tysch/stm32-geiger/Hardware/Main PCB/Main_PCB_overview.png

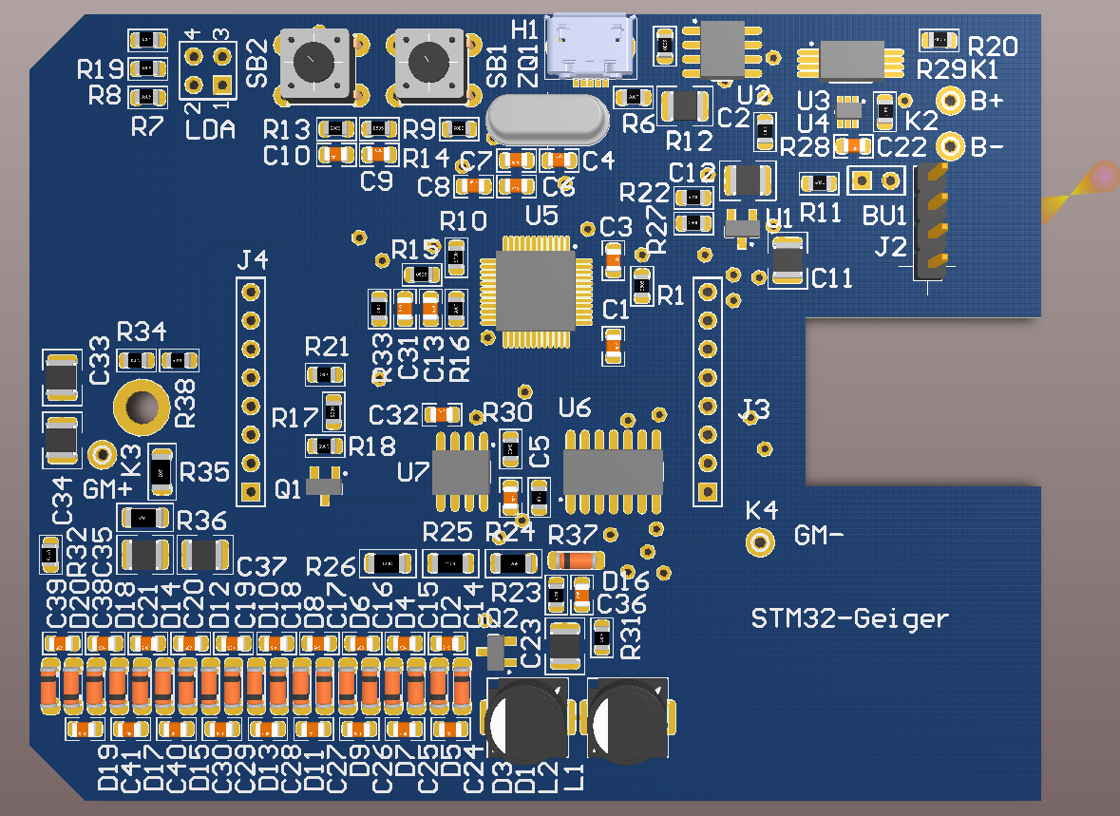
Hardware/Main PCB/Main_PCB_overview.png
