tysch/stm32-geiger/Prototyping/Case_prototype/1.jpg

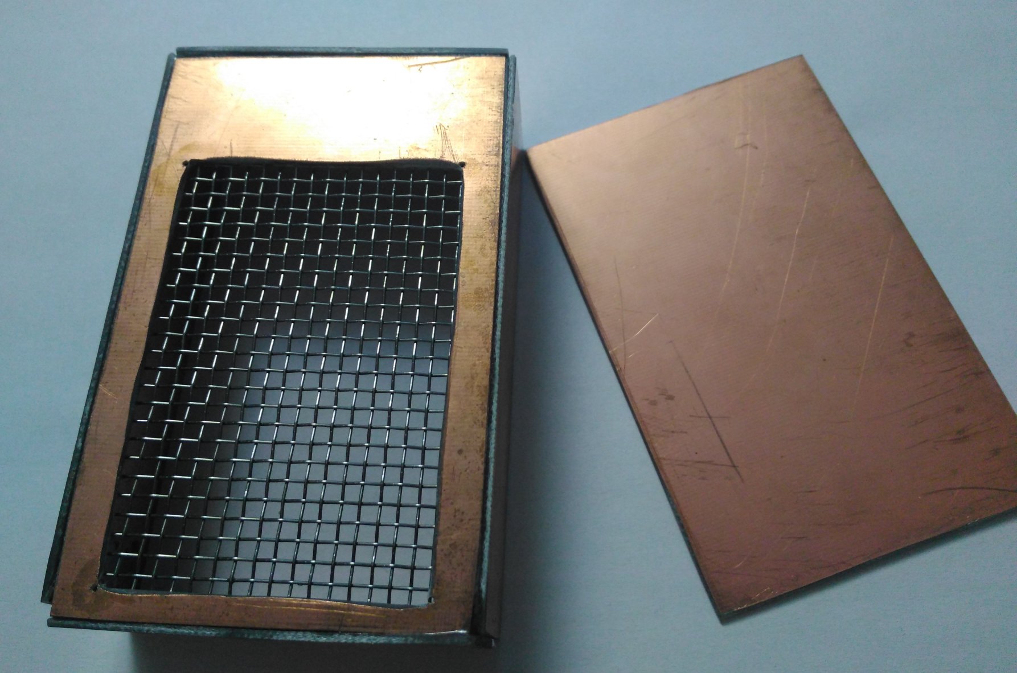
Prototyping/Case_prototype/1.jpg
