tysch/stm32-geiger/Prototyping/Case_prototype/2.jpg

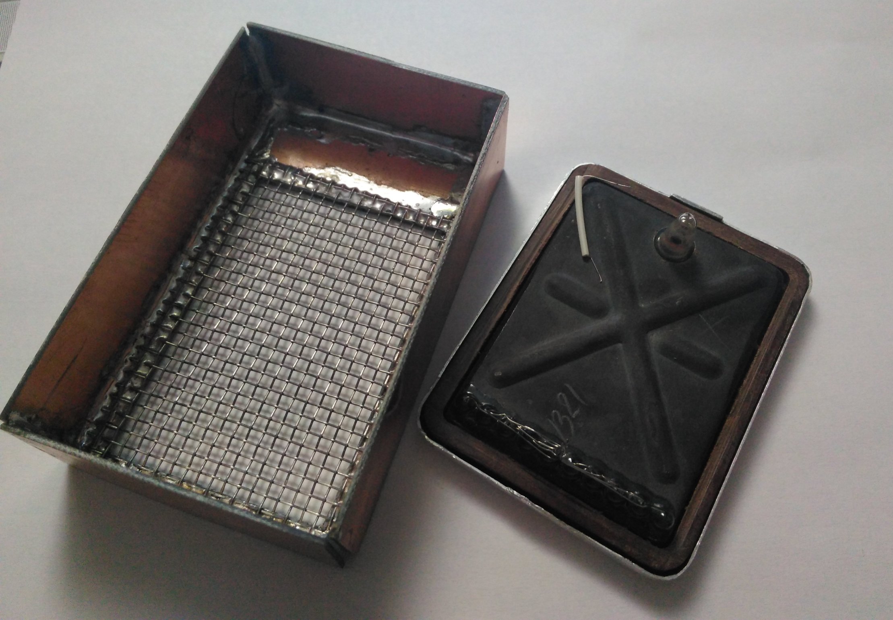
Prototyping/Case_prototype/2.jpg
