tysch/stm32-geiger/Prototyping/Case_prototype/3.jpg

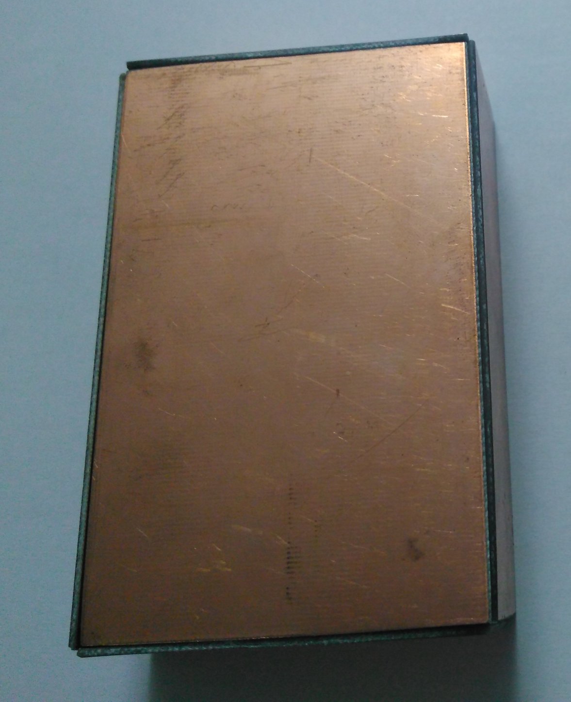
Prototyping/Case_prototype/3.jpg
