tysch/stm32-geiger/Prototyping/Case_prototype/4.jpg

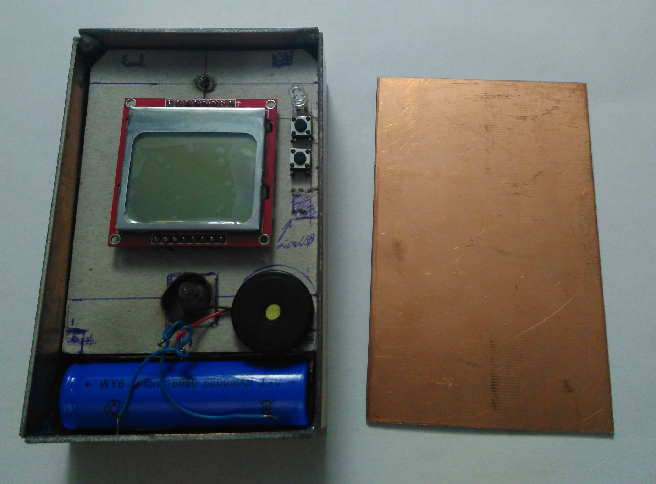
Prototyping/Case_prototype/4.jpg
