tysch/stm32-geiger/Case and assembly/1.jpg

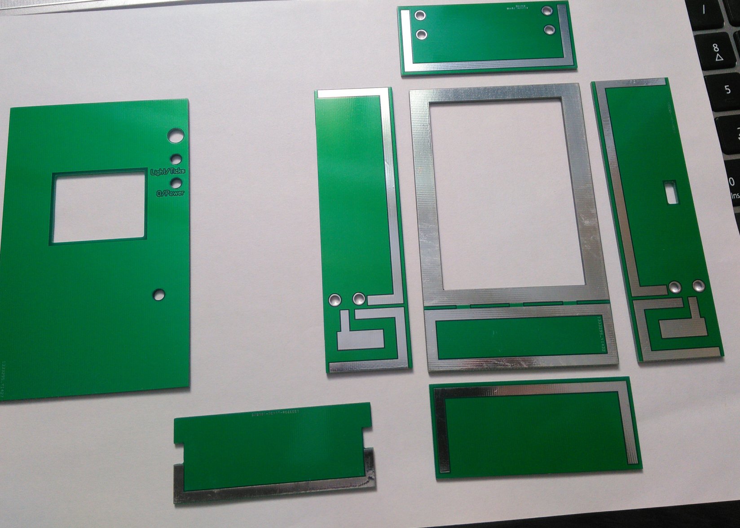
Case and assembly/1.jpg
