tysch/stm32-geiger/Case and assembly/2.jpg

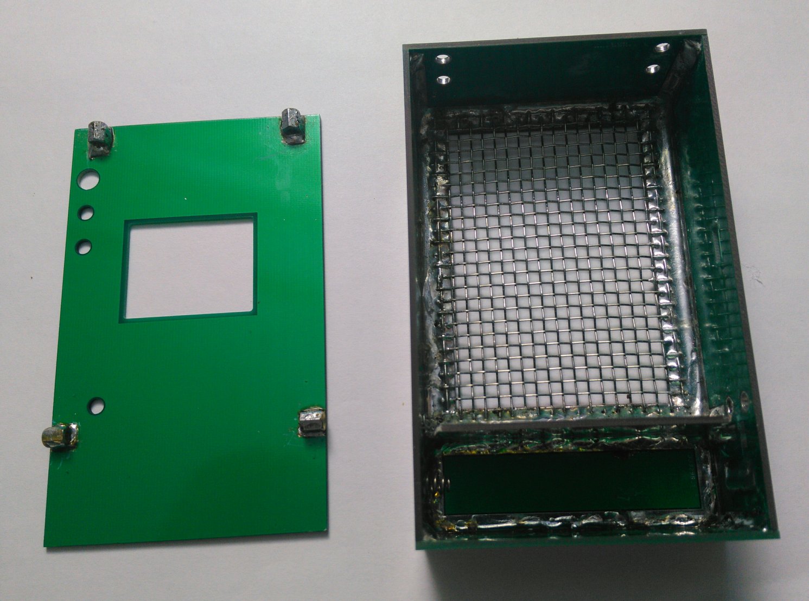
Case and assembly/2.jpg
