tysch/stm32-geiger/Case and assembly/3.jpg

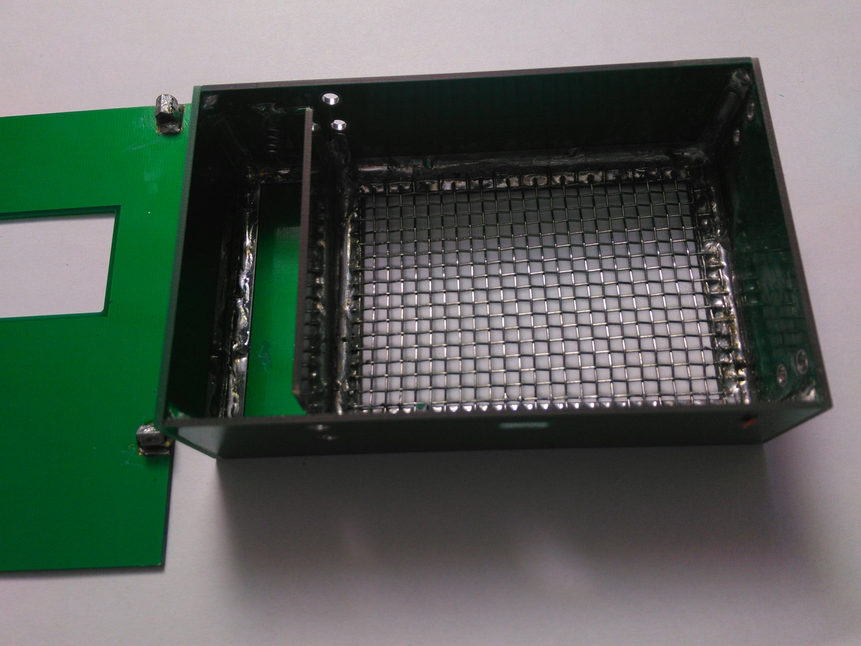
Case and assembly/3.jpg
