tysch/stm32-geiger/Case and assembly/4.jpg

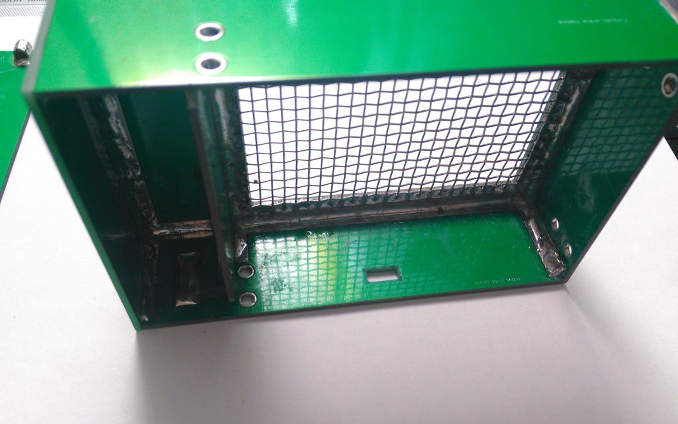
Case and assembly/4.jpg
