tysch/stm32-geiger/Case and assembly/5.jpg

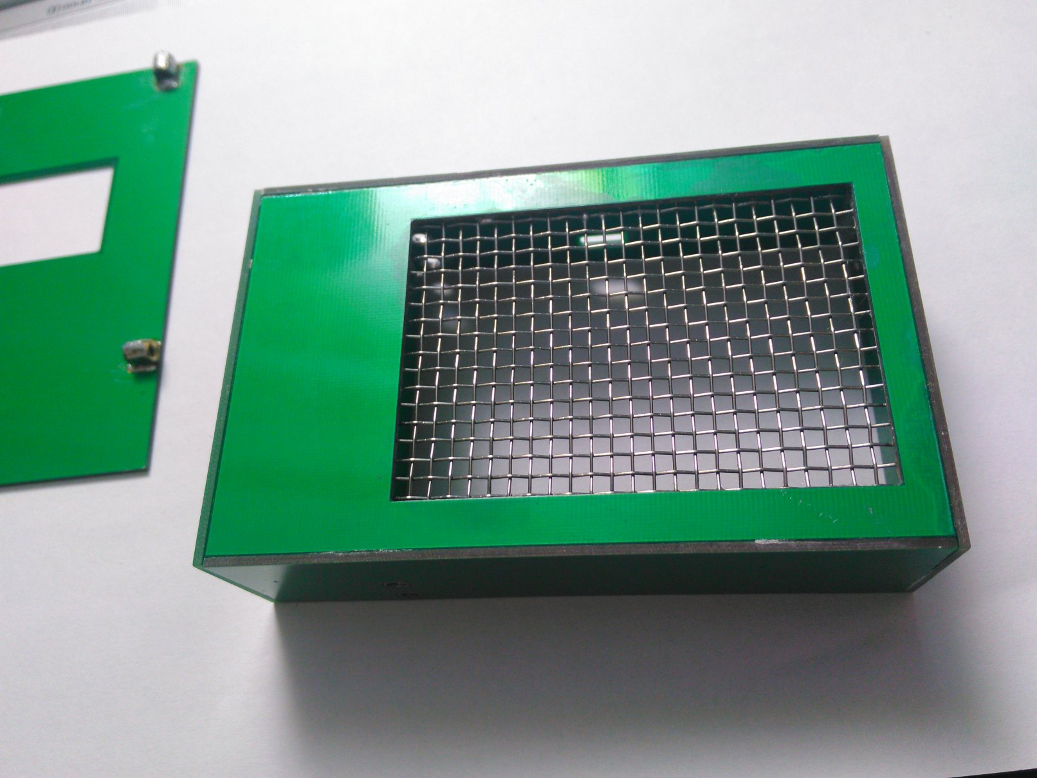
Case and assembly/5.jpg
