tysch/stm32-geiger/Case and assembly/6.jpg

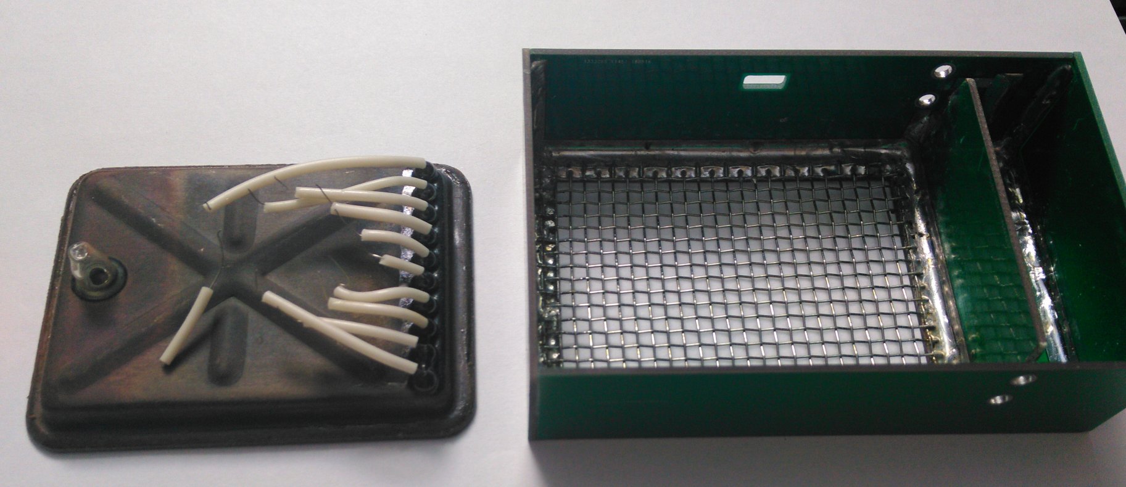
Case and assembly/6.jpg
