tysch/stm32-geiger/Case and assembly/7.jpg

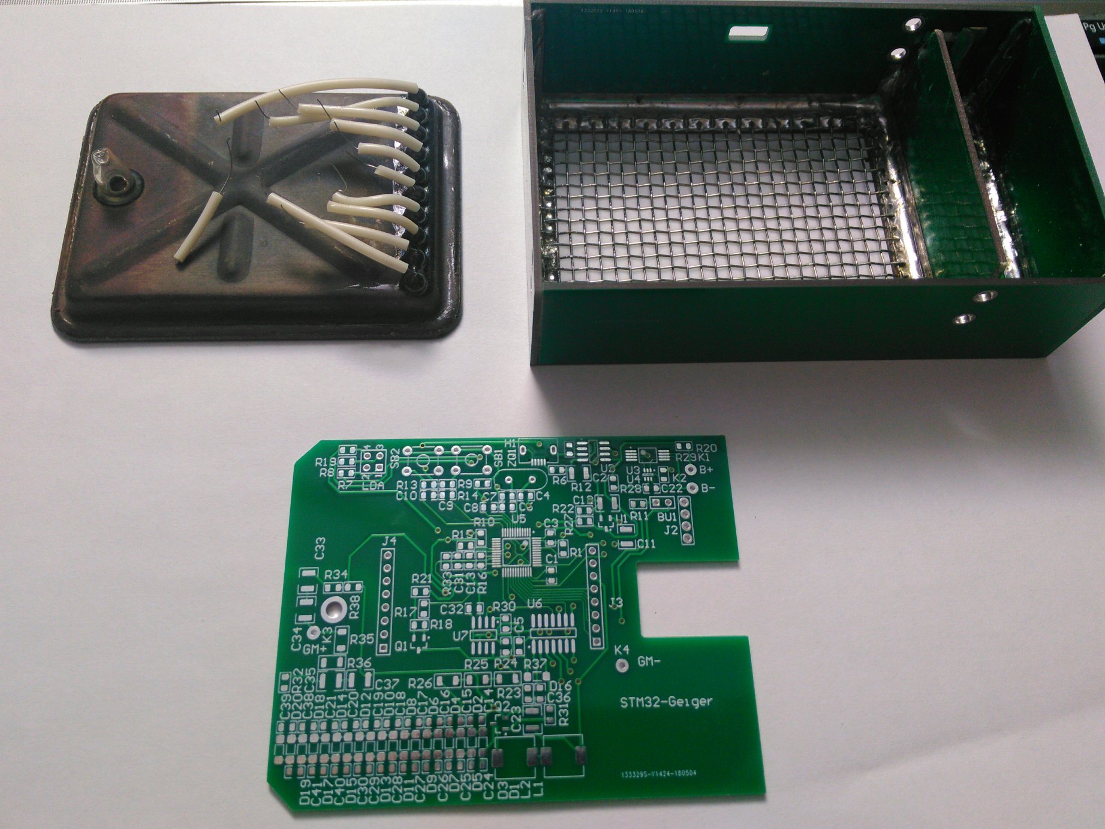
Case and assembly/7.jpg
