tysch/stm32-geiger/Case and assembly/9.jpg

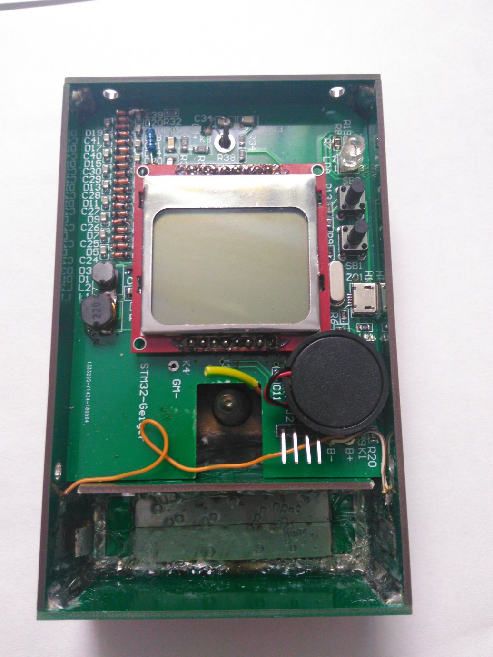
Case and assembly/9.jpg
