tysch/stm32-geiger/Case and assembly/10.jpg

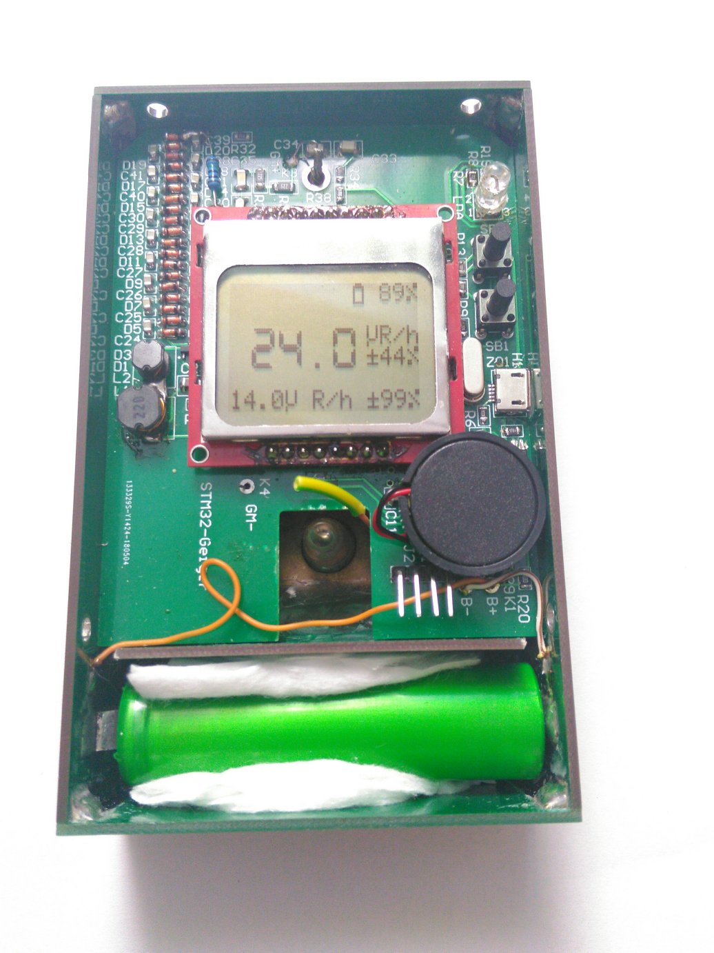
Case and assembly/10.jpg
