tysch/stm32-geiger/Case and assembly/11.jpg

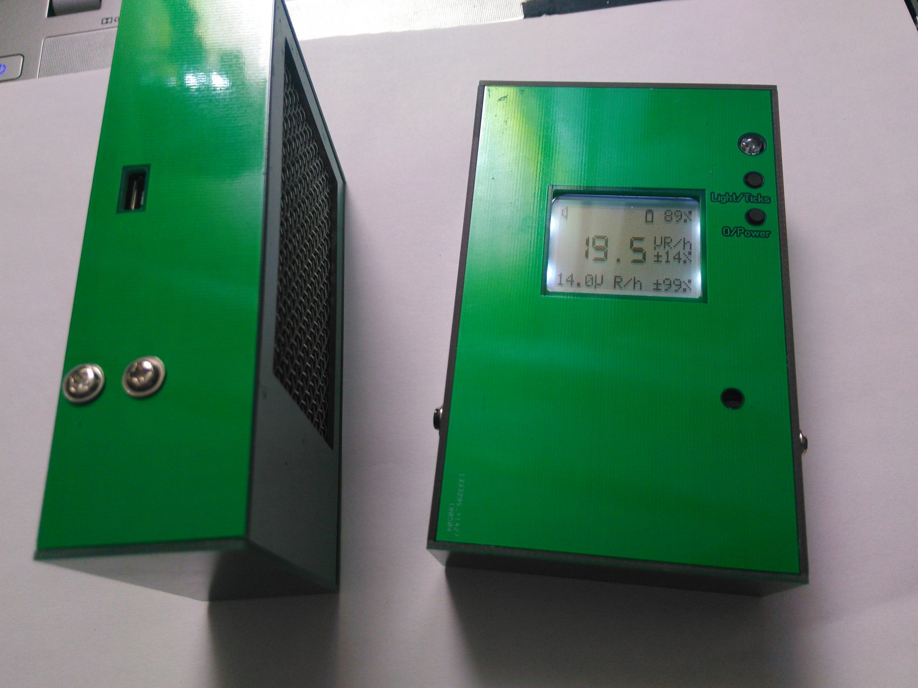
Case and assembly/11.jpg
