tysch/stm32-geiger/Case and assembly/12.jpg

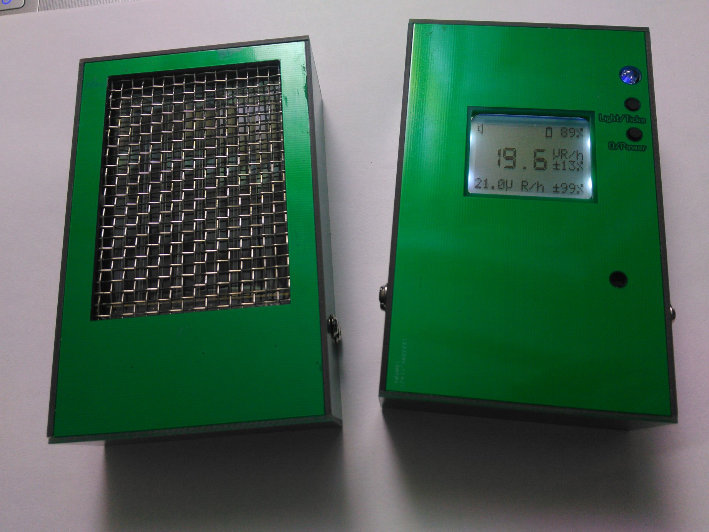
Case and assembly/12.jpg
