tysch/stm32-geiger/Case and assembly/14.jpg

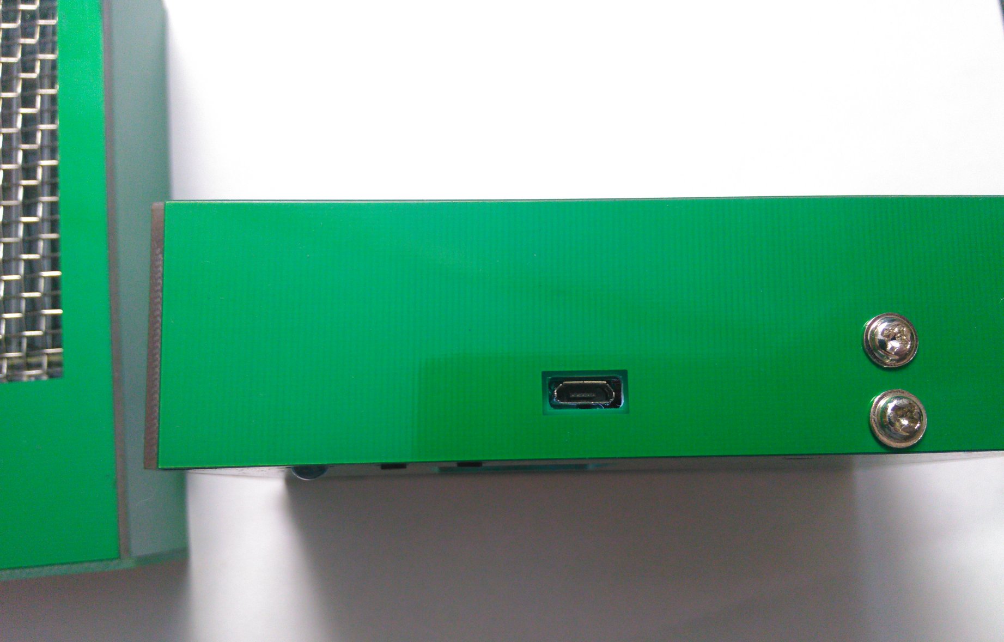
Case and assembly/14.jpg
