tysch/stm32-geiger/Case and assembly/15.jpg

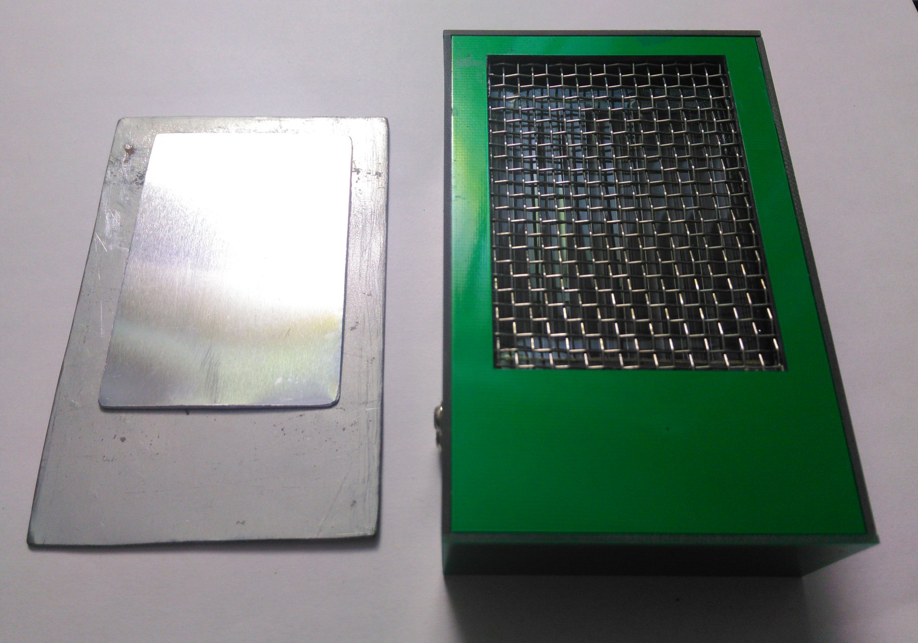
Case and assembly/15.jpg
