tysch/stm32-geiger/Case and assembly/16.jpg

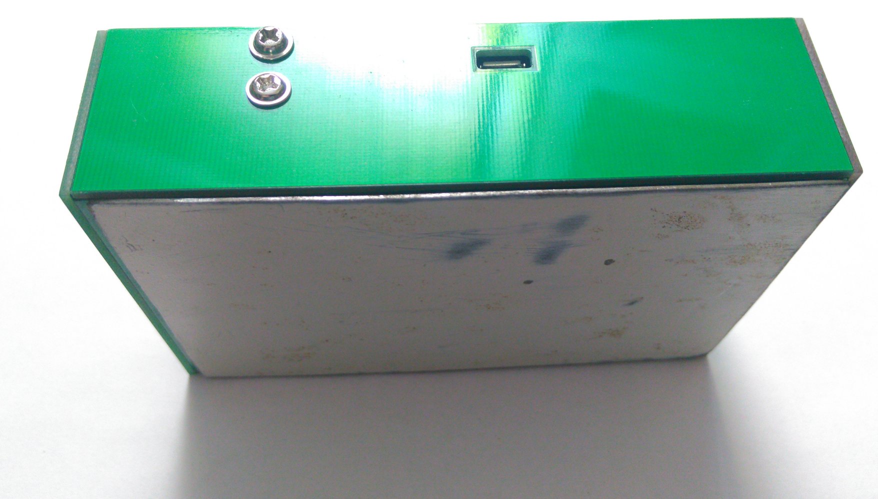
Case and assembly/16.jpg
