tysch/stm32-geiger/Case and assembly/Case_Drawing/Case_outer walls.jpg

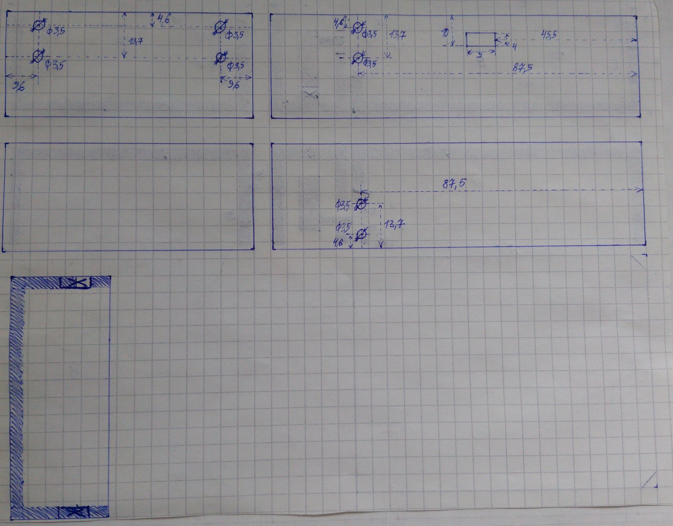
Case and assembly/Case_Drawing/Case_outer walls.jpg
