tysch/stm32-geiger/Case and assembly/Case_Drawing/Case_walls_spacer.jpg

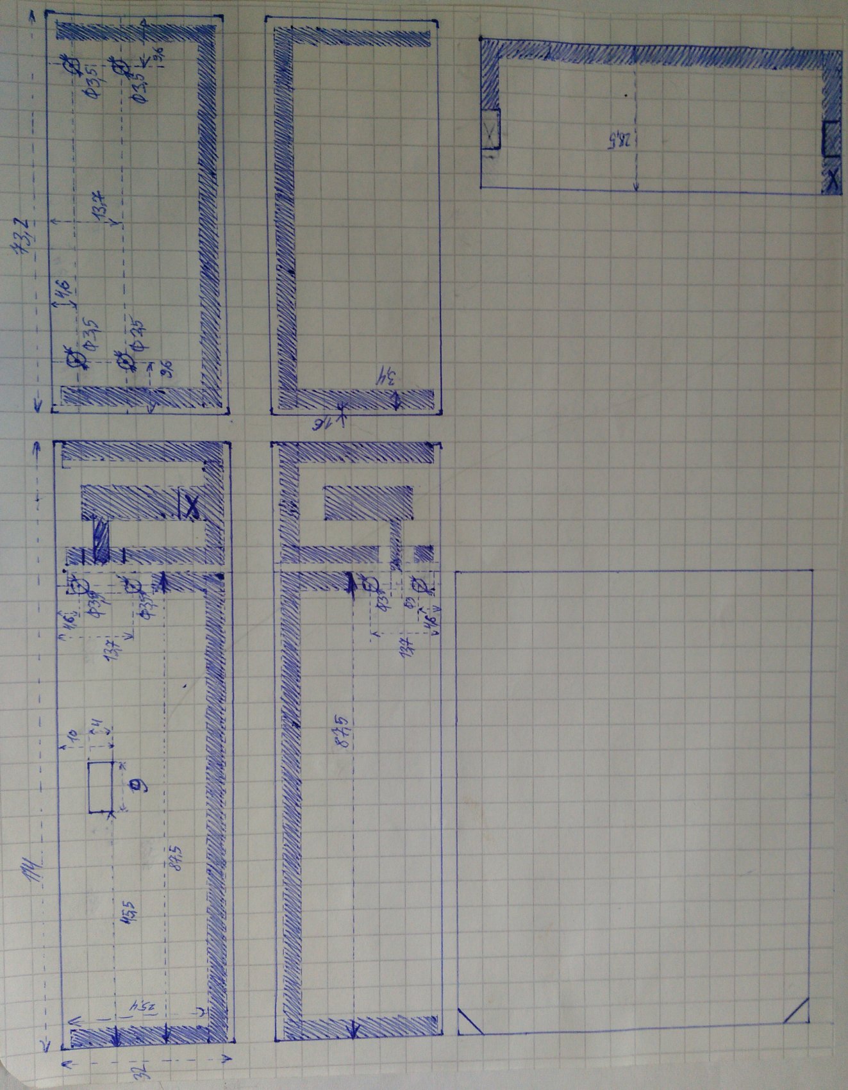
Case and assembly/Case_Drawing/Case_walls_spacer.jpg
