tysch/stm32-geiger/Test results/ambient.jpg

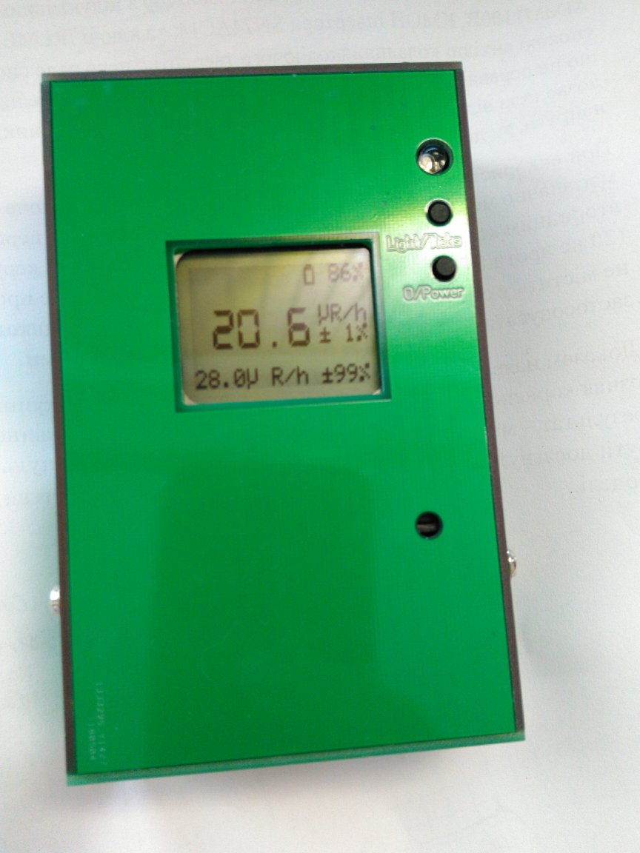
Test results/ambient.jpg
