tysch/stm32-geiger/Test results/potassium_fertilizer_beta+gamma.jpg

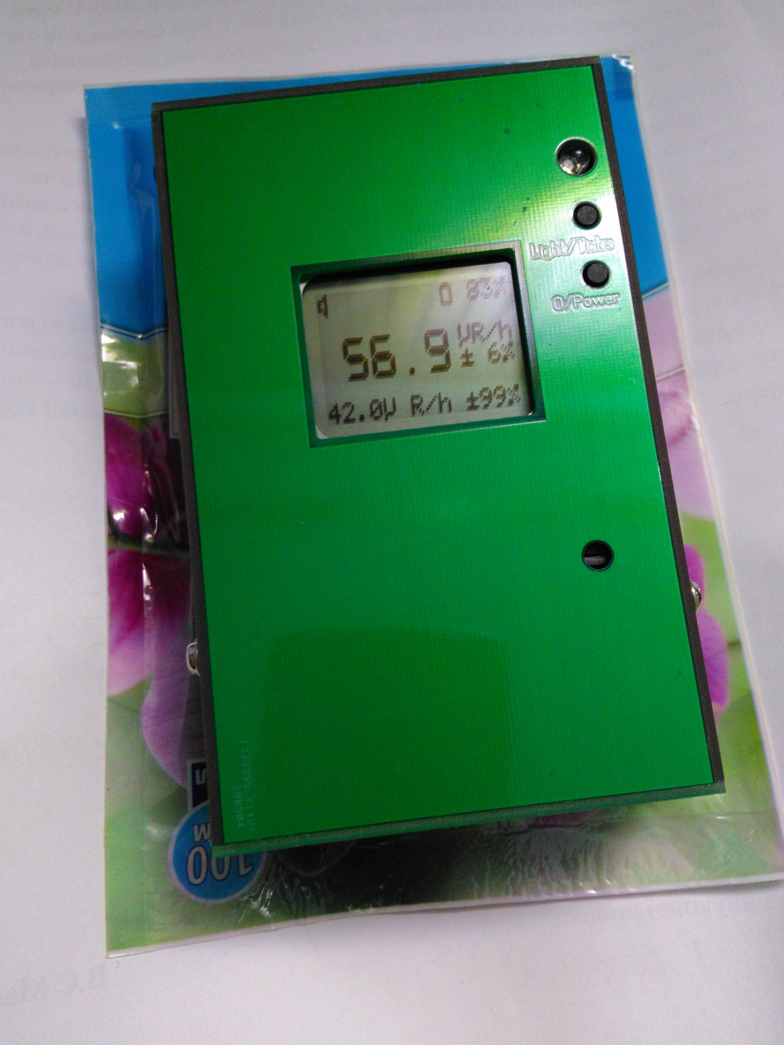
Test results/potassium_fertilizer_beta+gamma.jpg
