tysch/stm32-geiger/Test results/potassium_fertilizer_only_gamma.jpg

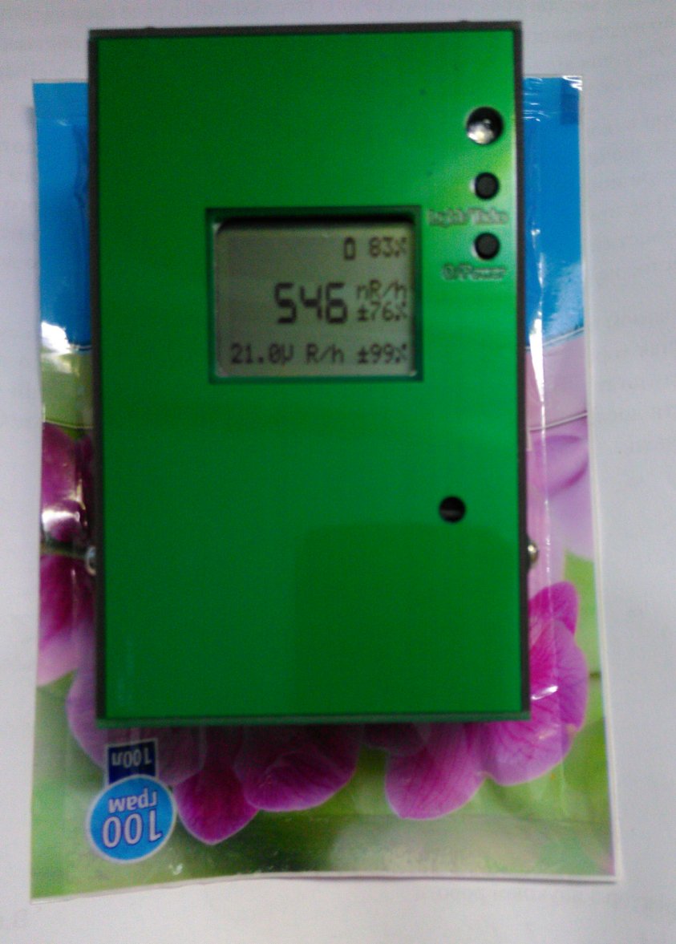
Test results/potassium_fertilizer_only_gamma.jpg
