tysch/stm32-geiger/Firmware/filters.c

#include <stdint.h>

#define NULL         0
#define STOPPER   0 // Smaller than any datum
#define MEDIAN_FILTER_SIZE 5

uint32_t median_filter(uint32_t datum)
{
    struct pair
    {
        struct pair *point; // Pointers forming list linked in sorted order
        uint32_t value;     // Values to sort
    };

    // Buffer of nwidth pairs
    static struct pair buffer[MEDIAN_FILTER_SIZE] = {{0}};
    // Pointer into circular buffer of data
     static struct pair *datpoint = buffer; 
    // Chain stopper
    static struct pair small = {NULL, STOPPER};
    // Pointer to head (largest) of linked list.
    static struct pair big = {&small, 0}; 

    // Pointer to successor of replaced data item
    struct pair *successor; 
    // Pointer used to scan down the sorted list
    struct pair *scan; 
    // Previous value of scan
    struct pair *scanold;
    // Pointer to median
    struct pair *median; 
    uint32_t i;

    if(datum == STOPPER)
    {
        datum = STOPPER + 1; // No stoppers allowed.
    }

    if((++datpoint - buffer) >= MEDIAN_FILTER_SIZE)
    {
        datpoint = buffer; // Increment and wrap data in pointer.
    }

    datpoint->value = datum; // Copy in new datum
    successor = datpoint->point; // Save pointer to old value's successor
    median = &big; // Median initially to first in chain
    scanold = NULL; // Scanold initially null.
    scan = &big; // Points to pointer to first (largest) datum in chain

    // Handle chain-out of first item in chain as special case
    if(scan->point == datpoint)
    {
        scan->point = successor;
    }

    scanold = scan;     // Save this pointer and
    scan = scan->point; // step down chain

    // Loop through the chain, normal loop exit via break.
    for(i = 0 ; i < MEDIAN_FILTER_SIZE; ++i)
    {
        // Handle odd-numbered item in chain
        if(scan->point == datpoint)
        {
            scan->point = successor; // Chain out the old datum.
        }

        if(scan->value < datum)
        { // If datum is larger than scanned value
            datpoint->point = scanold->point; // Chain it in here
            scanold->point = datpoint; // Mark it chained in.
            datum = STOPPER;
        }

        // Step median pointer down chain after doing odd-numbered element
        median = median->point; // Step median pointer.

        if(scan == &small) break; // Break at end of chain

        scanold = scan; // Save this pointer and
        scan = scan->point; // step down chain

        // Handle even-numbered item in chain.
        if(scan->point == datpoint)
        {
            scan->point = successor;
        }

        if (scan->value < datum)
        {
            datpoint->point = scanold->point;
            scanold->point = datpoint;
            datum = STOPPER;
        }

        if(scan == &small)  break;

        scanold = scan;
        scan = scan->point;
    }
    return median->value;
}

uint32_t exp_filter( uint32_t count)
{
    const char N_AVG = 9;   // 2^N counts to decay
    static uint64_t j = 0;
    static uint32_t round = 0;
    j = (j << N_AVG) - j + count + round;
    round = j % (1 << N_AVG);
    j = (j >> N_AVG);
    return (uint32_t) j;
}
